MarcoCaianiello/Glove-Exo-Prosthetics/Latching_mechanism/Locker mechanism/Progetto locker-senza bottone/Scatola di fissaggio v1.stl

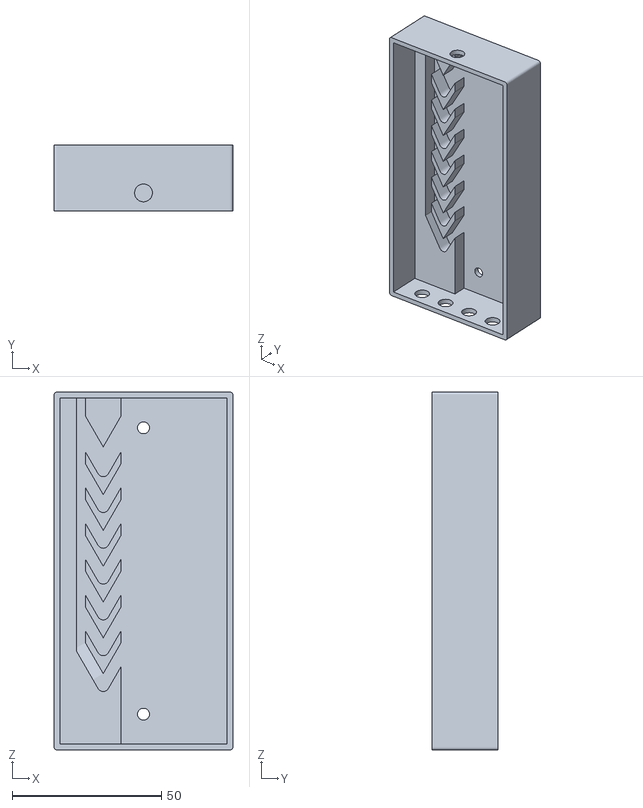
[picture p15: CAD file, 2023-07-07]
Latching_mechanism/Locker mechanism/Progetto locker-senza bottone/Scatola di fissaggio v1.stl
60.0 x 22.0 x 120.0
