MarcoCaianiello/Glove-Exo-Prosthetics/Latching_mechanism/openbionics/Triangle.STL

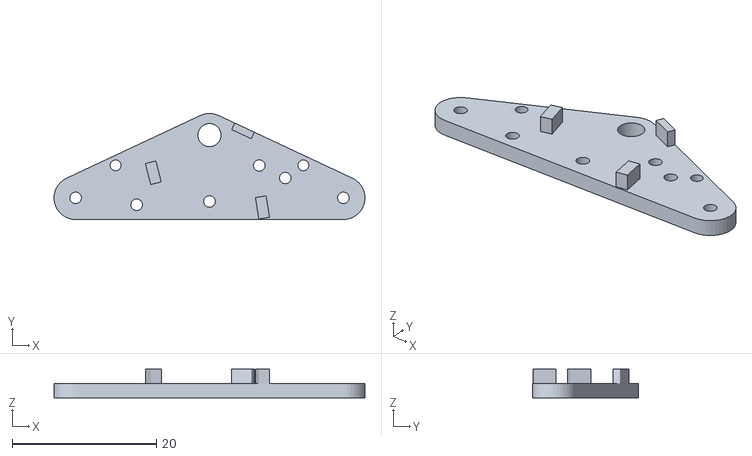
[picture p16: CAD file, 2023-01-29]
Latching_mechanism/openbionics/Triangle.STL
43.1 x 14.7 x 4.00
