MarcoCaianiello/Glove-Exo-Prosthetics/Tendon_guide/anchor_ring.stl

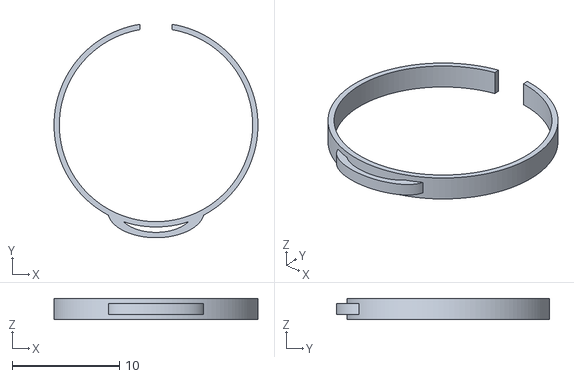
[picture p17: CAD file, 2023-02-17]
Tendon_guide/anchor_ring.stl
19.0 x 19.9 x 2.00
