MarcoCaianiello/Glove-Exo-Prosthetics/Latching_mechanism/openbionics/Pulley 3.STL

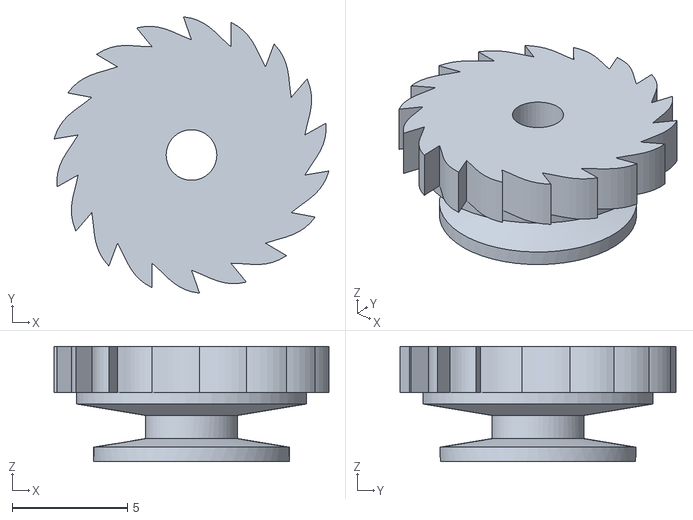
[picture p18: CAD file, 2023-01-29]
Latching_mechanism/openbionics/Pulley 3.STL
11.9 x 12.0 x 5.00
