MarcoCaianiello/Glove-Exo-Prosthetics/Thumb_Base_Wrist/Thumb_Wrist_Support_part1.stl

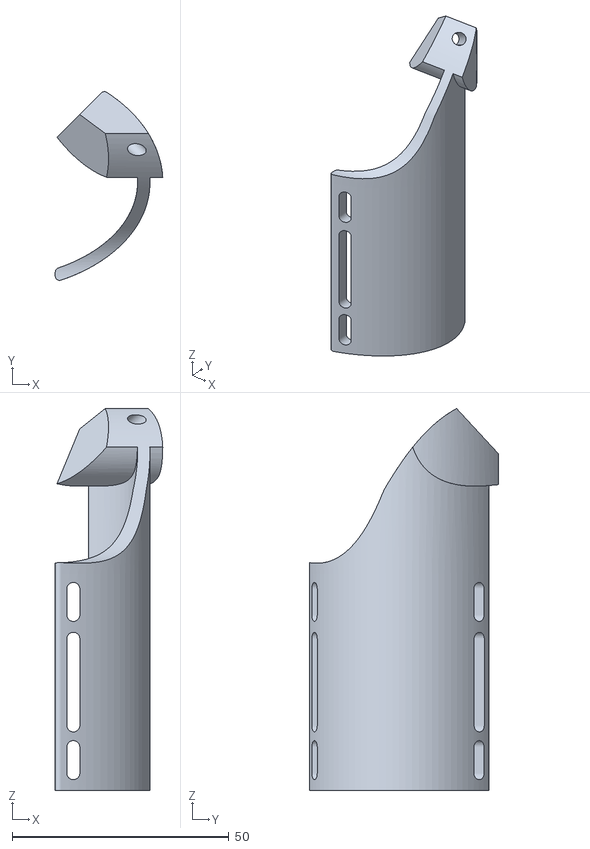
[picture p19: CAD file, 2023-07-07]
Thumb_Base_Wrist/Thumb_Wrist_Support_part1.stl
24.8 x 43.5 x 88.1
