MarcoCaianiello/Glove-Exo-Prosthetics/Latching_mechanism/openbionics/RAIL.stl

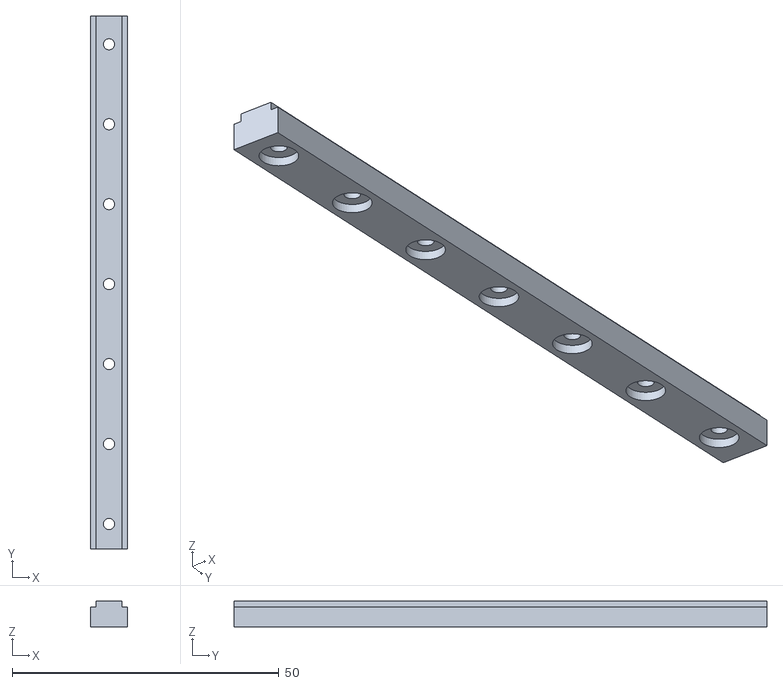
[picture p20: CAD file, 2023-01-29]
Latching_mechanism/openbionics/RAIL.stl
7.00 x 100.0 x 4.80
