MarcoCaianiello/Glove-Exo-Prosthetics/Latching_mechanism/openbionics/Back attachment.STL

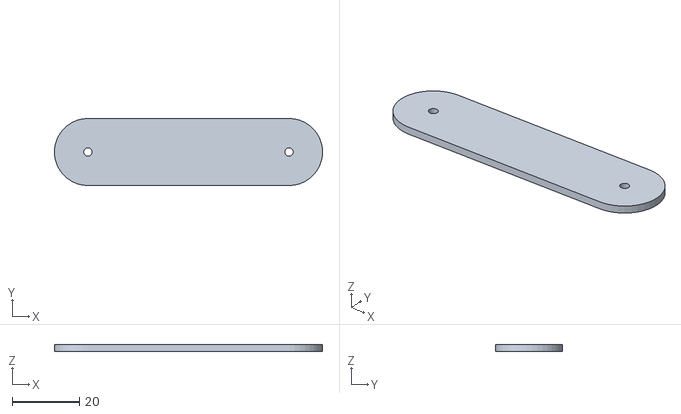
[picture p21: CAD file, 2023-01-29]
Latching_mechanism/openbionics/Back attachment.STL
79.9 x 20.0 x 2.00
