MarcoCaianiello/Glove-Exo-Prosthetics/Thumb_Base_Wrist/Tendon_Lock_Base v1.stl

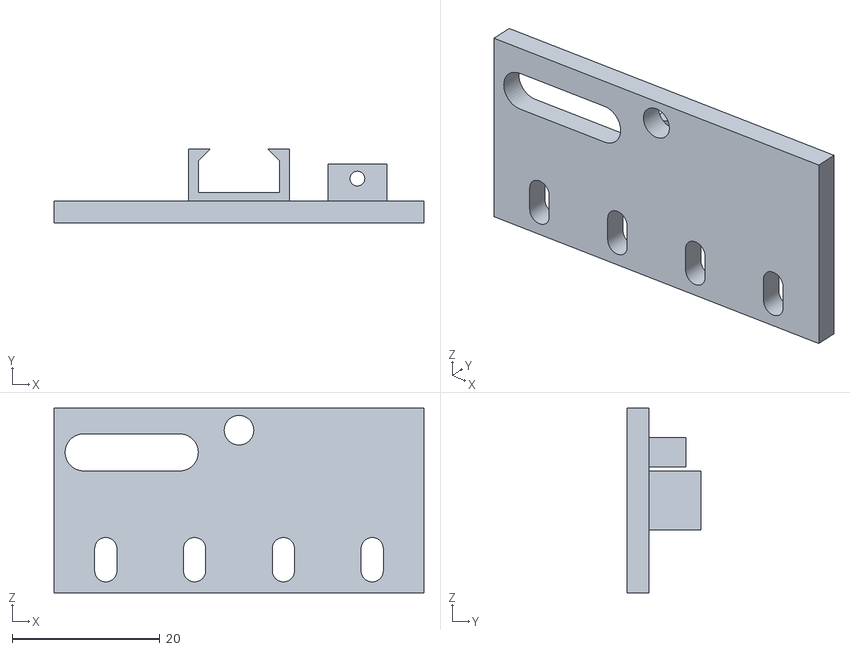
[picture p22: CAD file, 2023-07-07]
Thumb_Base_Wrist/Tendon_Lock_Base v1.stl
50.0 x 10.0 x 25.0
