MarcoCaianiello/Glove-Exo-Prosthetics/Latching_mechanism/openbionics/Ratchet 3.STL

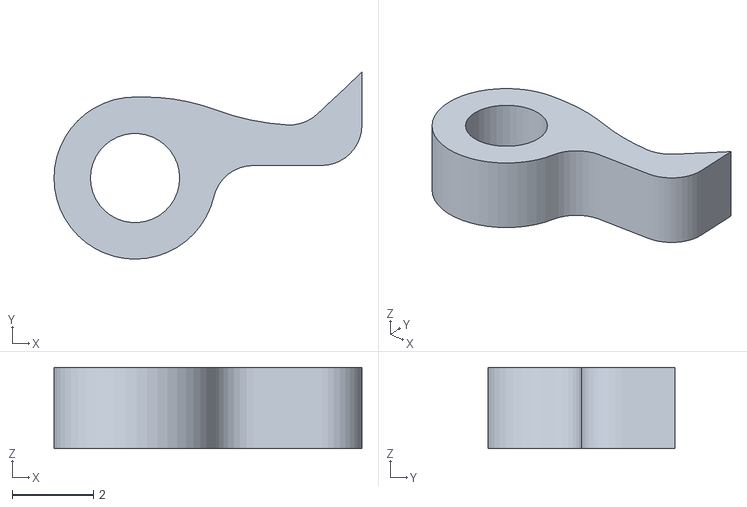
[picture p23: CAD file, 2023-01-29]
Latching_mechanism/openbionics/Ratchet 3.STL
7.60 x 4.62 x 2.00
