MarcoCaianiello/Glove-Exo-Prosthetics/Latching_mechanism/openbionics/Lever.STL

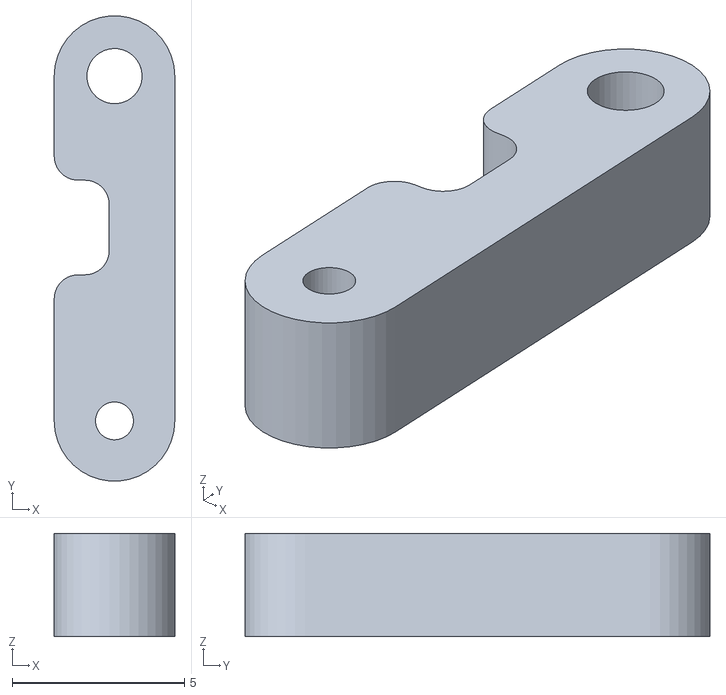
[picture p24: CAD file, 2023-01-29]
Latching_mechanism/openbionics/Lever.STL
3.50 x 13.5 x 3.00
