MarcoCaianiello/Glove-Exo-Prosthetics/Thumb_Base_Wrist/Thumb_Wrist_Support_part1_part2.stl

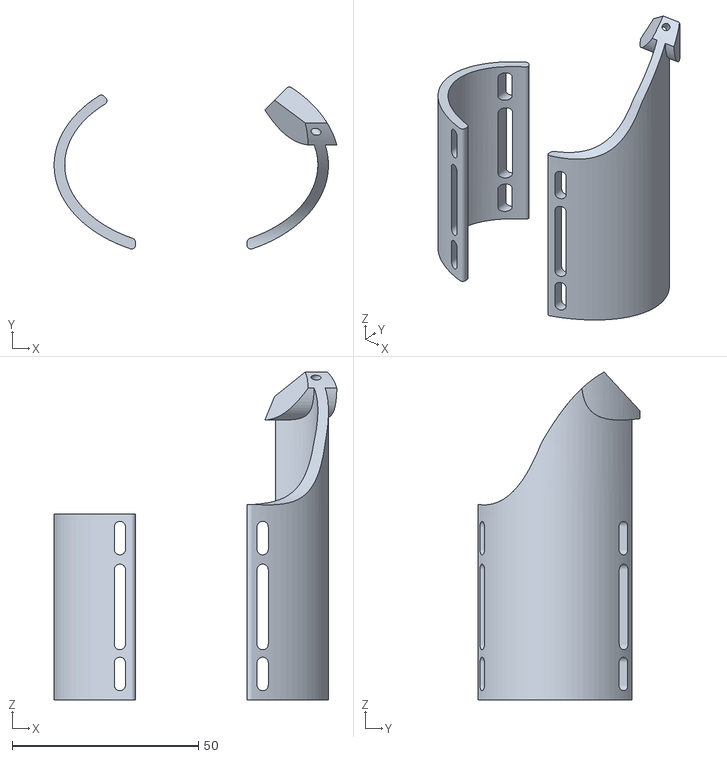
[picture p25: CAD file, 2023-07-07]
Thumb_Base_Wrist/Thumb_Wrist_Support_part1_part2.stl
76.0 x 43.5 x 88.1
