MarcoCaianiello/Glove-Exo-Prosthetics/Thumb_Base_Wrist/Thumb_Base_mod v2.stl

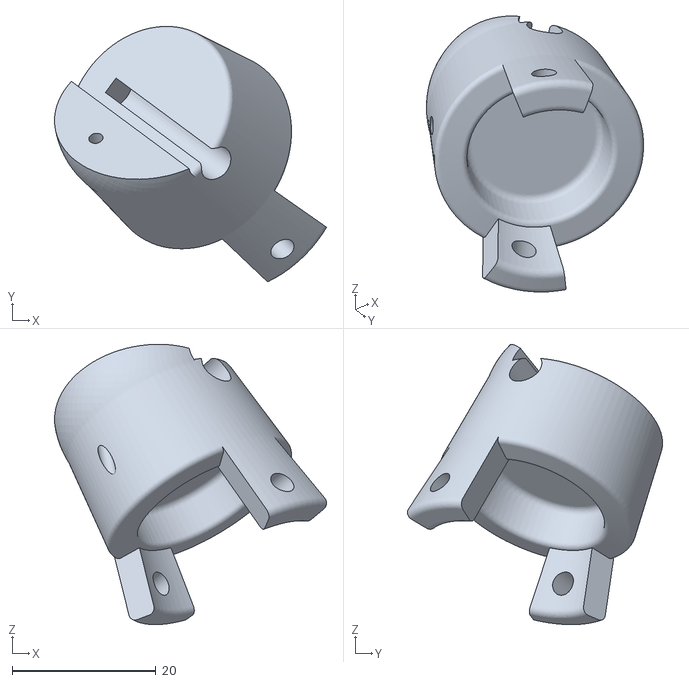
[picture p26: CAD file, 2023-07-07]
Thumb_Base_Wrist/Thumb_Base_mod v2.stl
37.8 x 35.4 x 38.9
