MarcoCaianiello/Glove-Exo-Prosthetics/Thumb_Base_Wrist/Thumb_Base v3.stl

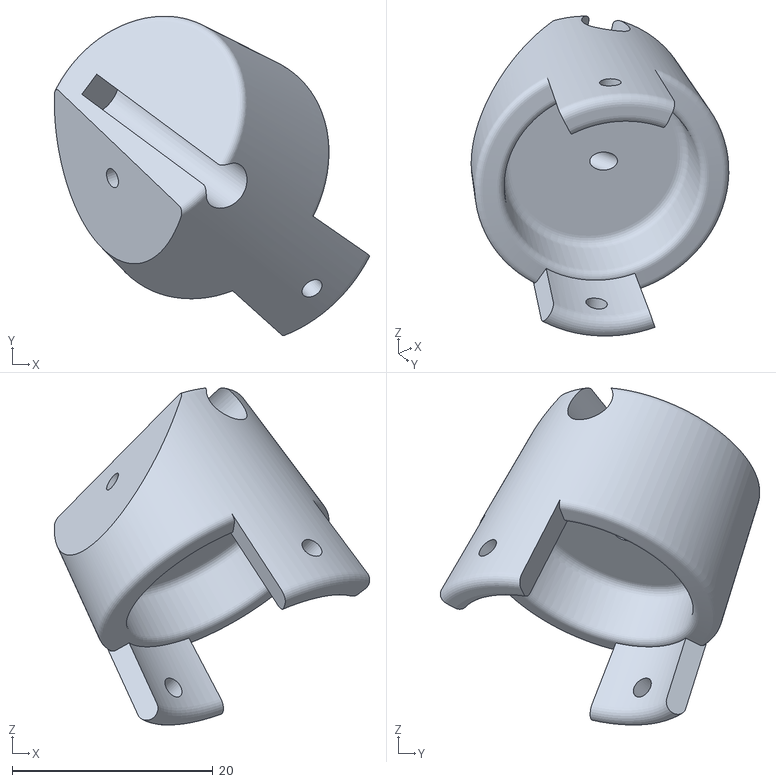
[picture p27: CAD file, 2023-07-07]
Thumb_Base_Wrist/Thumb_Base v3.stl
31.4 x 31.8 x 33.6
