MarcoCaianiello/Glove-Exo-Prosthetics/Thumb_Base_Wrist/Tendon_Lock_Base_Button v1.stl

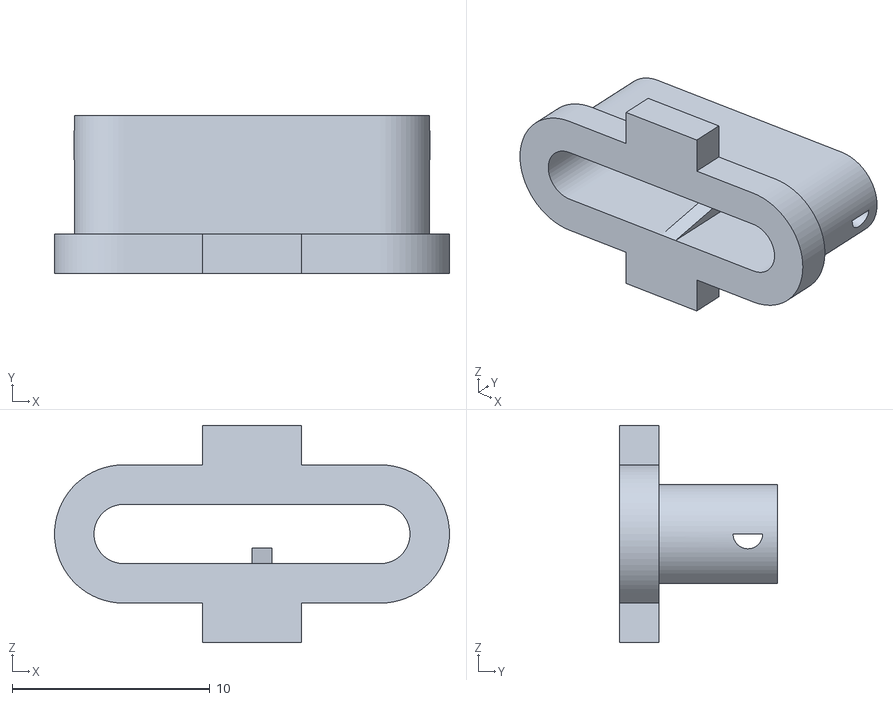
[picture p28: CAD file, 2023-07-07]
Thumb_Base_Wrist/Tendon_Lock_Base_Button v1.stl
20.0 x 8.00 x 11.0
